4cello/NotificationEgg/resources/phone.png

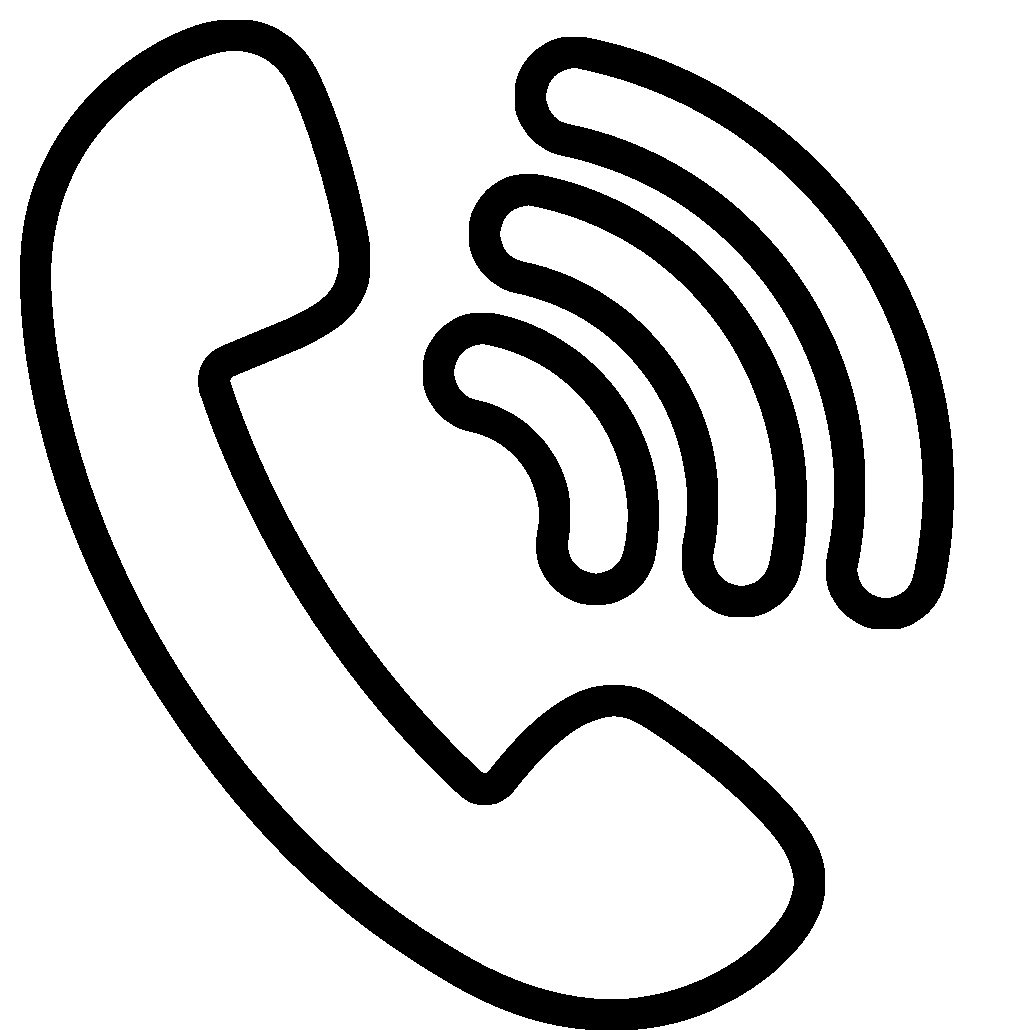
resources/phone.png
